quantumcompiler32/Blip_hackpad/.scratch/blip-foundation/orchestrator-status.md

# Blip Foundation orchestrator status

## Batch 1 — 2026-07-28

### Local ticket to GitHub issue mapping

| Local | GitHub | Ticket |
| --- | ---: | --- |
| 01 | #2 | Establish the authoritative Blip hardware baseline |
| 02 | #3 | Apply minimal controller, power, and display corrections |
| 03 | #4 | Pass and document the Hardware Validation Gate |
| 04 | #5 | Prove the simulator-to-Agent tracer bullet |
| 05 | #6 | Prove the bundled Agent lifecycle and private IPC |
| 06 | #7 | Configure and persist the three stable Profiles |
| 07 | #8 | Execute safe versioned actions end to end |
| 08 | #9 | Ship the production Control Center foundation |
| 09 | #10 | Compose prioritized status for both displays |
| 10 | #11 | Persist Pomodoro and deliver DND-aware alarms |
| 11 | #12 | Deliver Context Browser and essential media behavior |
| 12 | #13 | Connect physical firmware and Offline Controls |
| 13 | #14 | Render semantic scenes on the physical displays |
| 14 | #15 | Pass the complete Foundation Release gate |

### Batch result

- #2 was selected as the only safely eligible ticket.
- Its full implementation was already integrated on `main` in `4b0bf7952dc8dd03a1a6d97fd9f9920f9e01b90a`.
- Independent acceptance, Standards, and Spec reviews found no gap and no unrelated change.
- No new implementation or merge was required.
- GitHub #2 was closed on 2026-07-28 after explicit user approval; `ready-for-agent` was removed and the verified commit/test evidence was posted.

### Post-batch issue #5 completion — 2026-07-28

- The user-owned issue #5 work was preserved on `codex/issue-5-simulator-agent-tracer`, completed, and committed as `46f13ef88c62ae5f621bffd2c9d91d3740e414b7`.
- Standards and Spec reviews reported zero remaining findings after the device-relative timestamp correction.
- The commit was fast-forwarded into `main`, verified on the integrated state, and pushed to `origin/main`.
- GitHub #5 was closed after remote integration was confirmed; `ready-for-agent` was removed and test evidence was posted.
- No issue #6 implementation work was started.

### Tickets still in progress

- #3 implementation is present in `221bb3c`, but GitHub remains open with a Hardware Validation Gate criterion outstanding.
- #4 automated evidence is present in `28ab1d5`, but GitHub remains open pending human physical/visual manufacturing sign-off.

### Branches and commits

| Ticket | Branch | Commit | State |
| --- | --- | --- | --- |
| #2 | `codex/issue-2-hardware-baseline` | `4b0bf7952dc8dd03a1a6d97fd9f9920f9e01b90a` | Existing commit verified; branch/worktree clean; already in `main` |
| #5 | `codex/issue-5-simulator-agent-tracer` | `46f13ef88c62ae5f621bffd2c9d91d3740e414b7` | Integrated into and pushed on `main`; GitHub issue closed |

Issue #2 worktree: `/private/tmp/blip-issue-2-batch-1`.

### Tests run

- `sh scripts/verify-hardware-source-of-truth.sh` — passed.
- `sh scripts/verify-minimal-pcb-corrections.sh` — passed.
- `sh scripts/verify-hardware-validation-gate.sh` — passed with human sign-off explicitly still required.
- Historical issue #2 diff whitespace check — passed.
- Issue #2 implementation ancestor check against current `HEAD` — passed.
- Agent also verified a forbidden KiCad lock-file fixture is rejected and shell syntax checks pass.
- Issue #5 `npm test` — 5/5 passed on the branch and integrated `main`.
- Issue #5 strict TypeScript check — passed.
- Issue #5 JSON tracer scenario — passed.
- Issue #5 Control Center HTML diagnostic scenario — passed.
- Issue #5 `git diff --check` — passed.
- Issue #5 Standards review — zero remaining findings.
- Issue #5 Spec review — zero remaining findings.

### Open blockers

- #3/#4: final physical, visual, connector-height, clearance, and manufacturing review remains human-only.
- #6's declared #5 blocker is completed and integrated.
- #7 remains blocked by #6; #8 by #7; #9 by #6/#7/#8; #10 by #7.
- #11–#15 remain blocked by the declared upstream software and hardware tickets.

### Human actions required

1. Complete the Hardware Change Guide's physical/visual sign-off before #4 or manufacturing can be approved.

### Newly unblocked frontier

- #3's declared #2 blocker is resolved, although its implementation already exists and its remaining Hardware Validation Gate evidence is tracked by #4.
- #6 is now the next automatically verifiable Foundation critical-path ticket because #5 is closed and its commit is present on `origin/main`.

### Recommended next batch

- First choice: #6, subject to a fresh mandatory read-only preflight and explicit batch/model approval.
- Do not dispatch #7 or #10 until all of their declared blockers are completed and integrated.
- Keep #4 open until Moksh supplies the required human hardware evidence.

## Read-only preflight for the next batch — 2026-07-28

- No next batch has been launched.
- #5 (local 04) is closed and integrated on `origin/main` at `46f13ef88c62ae5f621bffd2c9d91d3740e414b7`.
- #6 (local 05) is open, labelled `ready-for-agent`, and its declared #5 blocker is completed and integrated.
- #3 and #4 are open without `ready-for-agent`; #4 also requires human hardware evidence.
- All other ready tickets retain at least one open declared blocker.
- Required next event: run the mandatory fresh read-only preflight and obtain explicit approval before creating a #6 worktree, branch, or agent.
