quantumcompiler32/Blip_hackpad/docs/adr/0004-bundle-control-center-and-agent.md

# Bundle Control Center and the Blip Agent

Blip ships as one macOS installation containing the visible Tauri Control Center and a bundled Blip Agent login-item helper. The Agent starts automatically, continues operating when the Control Center window is closed, and can open or focus Control Center when requested by the device. Users install, update, enable, disable, and uninstall Blip as one product rather than managing two independent applications.
